cmb87/project-bicopter/imgs/IMG-20210226-WA0008.jpeg

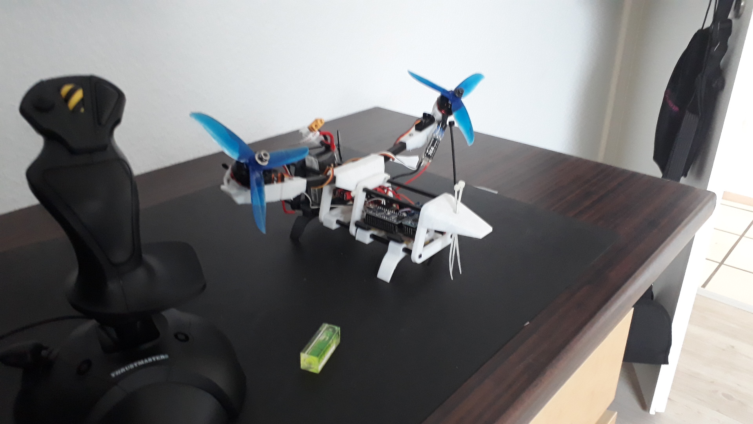
imgs/IMG-20210226-WA0008.jpeg
