cmb87/project-bicopter/imgs/inflight1.png

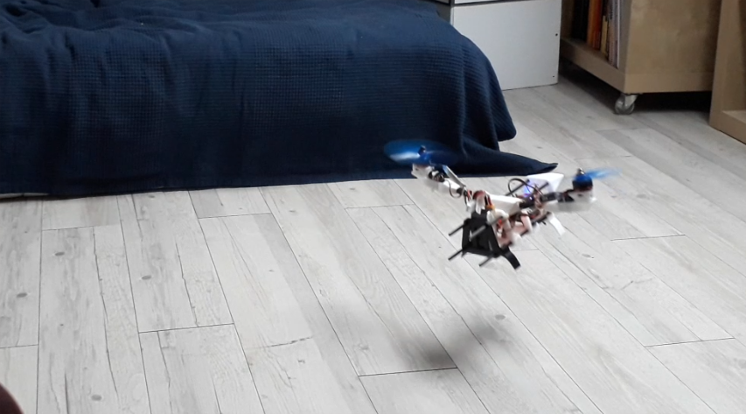
imgs/inflight1.png
