cmb87/project-bicopter/imgs/mw2.png

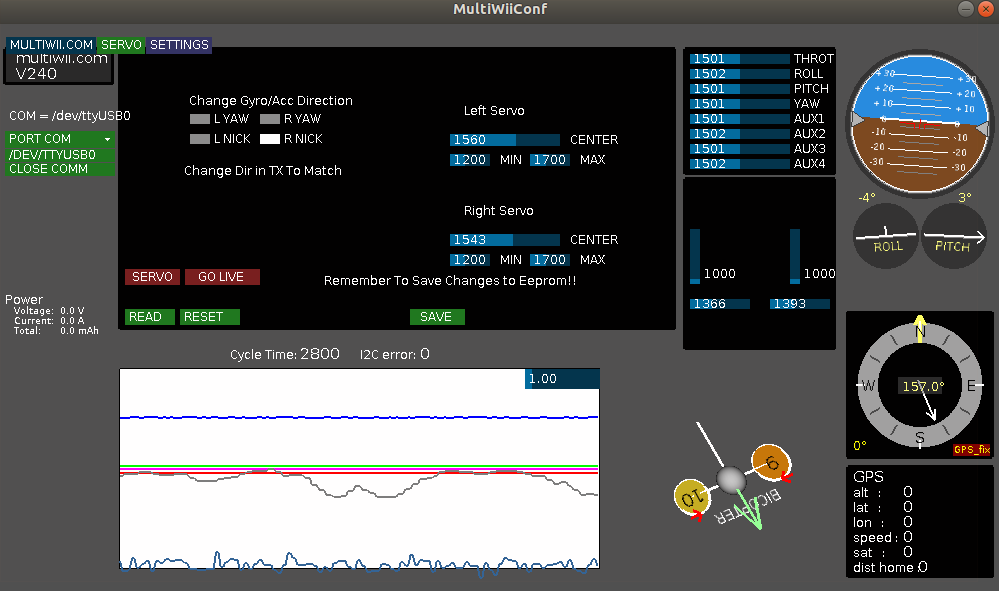
imgs/mw2.png
