cmb87/project-bicopter/construction/3dprinted/batteryBody.scad

t = 5;

rx = 100;
rdy = 4.1;
roy = 30;
royl = 50;

p0 = [0,0,18];
p1 = [0,25,18];
p2 = [40,15,18];
p3 = [40,0,18];

k = 12;


module rails(oz=2) {
    
  translate([-rx/2,roy/2,oz]) cube([rx,rdy,rdy]);
  mirror([0,1,0]){
    translate([-rx/2,roy/2,oz]) cube([rx,rdy,rdy]);
  }
    
}

module railsLow(oz=2) {
    
  translate([-rx/2,royl/2,oz]) cube([rx,rdy,rdy]);
  mirror([0,1,0]){
    translate([-rx/2,royl/2,oz]) cube([rx,rdy,rdy]);
  }
    
}


module span() {
difference(){
  hull(){
    translate([p0[0],p0[1],0])cylinder(r=p0[2]/2, h=t, $fn=20);
    translate([p1[0],p1[1],0])cylinder(r=p1[2]/2, h=t, $fn=20);
    translate([p2[0],p2[1],0])cylinder(r=p2[2]/2, h=t, $fn=20);
    translate([p3[0],p3[1],0])cylinder(r=p3[2]/2, h=t, $fn=20);
      
  }
  
  hull(){
    translate([p0[0]+3,p0[1]-3,-1])cylinder(r=p0[2]/k, h=2*t, $fn=20);
    translate([p1[0]+3,p1[1]-3,-1])cylinder(r=p1[2]/k, h=2*t, $fn=20);
    translate([p2[0]-3,p2[1]-3,-1])cylinder(r=p2[2]/k, h=2*t, $fn=20);
    translate([p3[0]-3,p3[1]-3,-1])cylinder(r=p3[2]/k, h=2*t, $fn=20);
  }

  translate([-120/2,-40,-1])cube([120,40,10]);
}
}


difference() {
rotate([0,-90,0])
union(){
  span();
  mirror([0,1,0])span();
};

translate([0,0,38])rails();
translate([0,0,-5])railsLow();

}

translate([-5,-10-7/2,-5])cube([3,7,50]);
translate([-5,+10-7/2,-5])cube([3,7,50]);
